quantdrent/Rien-Prescript-Beeper/firmware/ESP32/PrescriptBeeper/PixelifySans_Regular12pt7b.h

const uint8_t PixelifySans_Regular12pt7bBitmaps[] PROGMEM = {
  0x00, 0xFF, 0xFF, 0xFC, 0x3C, 0xC6, 0xC6, 0x21, 0x42, 0x30, 0xC3, 0x0C,
  0x30, 0xC3, 0x0C, 0x30, 0xCF, 0xFF, 0xFF, 0xF3, 0x0C, 0x30, 0xC3, 0x0C,
  0x30, 0xCF, 0xFF, 0xFF, 0xF3, 0x0C, 0x30, 0xC0, 0x06, 0x00, 0xC0, 0xFE,
  0x1F, 0xCC, 0x07, 0x80, 0xF0, 0x06, 0x00, 0xC0, 0x07, 0xF0, 0xFE, 0x00,
  0x30, 0x07, 0x80, 0xF0, 0x19, 0xFC, 0x3F, 0x80, 0xC0, 0x18, 0x03, 0x00,
  0x30, 0x03, 0x18, 0x01, 0xBF, 0x03, 0x1F, 0x81, 0x83, 0x07, 0x01, 0x83,
  0x00, 0x02, 0x00, 0x03, 0x00, 0x01, 0x80, 0x03, 0x03, 0x01, 0x81, 0x83,
  0x03, 0xF1, 0x81, 0xFB, 0x00, 0x31, 0x80, 0x18, 0x3F, 0x03, 0xF0, 0xC0,
  0xCC, 0x0C, 0x41, 0x03, 0x30, 0x33, 0x00, 0xC0, 0x0C, 0x03, 0x30, 0x33,
  0x0C, 0x0C, 0xC0, 0xC3, 0xF3, 0x3F, 0x30, 0xD8, 0xA0, 0x06, 0x0C, 0x18,
  0x31, 0x83, 0x06, 0x0C, 0x19, 0xC3, 0x06, 0x0C, 0x07, 0x06, 0x0C, 0x18,
  0x0C, 0x18, 0x30, 0x60, 0xC0, 0xC3, 0x0C, 0x30, 0x30, 0xC3, 0x0C, 0x30,
  0x30, 0xC3, 0x0C, 0xC3, 0x0C, 0x33, 0x0C, 0x30, 0xC3, 0x00, 0x5D, 0x50,
  0x0C, 0x03, 0x00, 0xC0, 0x30, 0x0C, 0x3F, 0xFF, 0xFC, 0x30, 0x0C, 0x03,
  0x00, 0xC0, 0xD8, 0xA0, 0xFF, 0xFC, 0xF0, 0x00, 0xC0, 0x60, 0x18, 0x0C,
  0x03, 0x01, 0x80, 0x60, 0x30, 0x0C, 0x06, 0x01, 0x80, 0xC0, 0x30, 0x18,
  0x06, 0x00, 0x3F, 0x87, 0xF3, 0x01, 0xE0, 0x3C, 0x07, 0x80, 0xF0, 0x1E,
  0x03, 0xC0, 0x78, 0x0F, 0x01, 0xE0, 0x3C, 0x06, 0x7F, 0x0F, 0xE0, 0x18,
  0x33, 0x9E, 0x30, 0x60, 0xC1, 0x83, 0x06, 0x0C, 0x18, 0x30, 0x60, 0xC1,
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
  {   616,  11,  15,  14,    1,  -14 },   // 0x47 'G'
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

const GFXfont PixelifySans_Regular12pt7b PROGMEM = {
  (uint8_t  *)PixelifySans_Regular12pt7bBitmaps,
  (GFXglyph *)PixelifySans_Regular12pt7bGlyphs,
  0x20, 0x7E, 24 };

// Approx. 2253 bytes
