quantdrent/Rien-Prescript-Beeper/firmware/ESP32/PrescriptBeeper/PixelifySans_Regular20pt7b.h

const uint8_t PixelifySans_Regular20pt7bBitmaps[] PROGMEM = {
  0x00, 0xFF, 0xFF, 0xFF, 0xFF, 0xFF, 0xFF, 0xFF, 0xFF, 0xFF, 0x00, 0x0F,
  0xFF, 0xF0, 0xF0, 0xF3, 0xC3, 0xCF, 0x0F, 0x3C, 0x3C, 0x0C, 0x0C, 0x30,
  0x33, 0x03, 0x0C, 0x0C, 0x1E, 0x07, 0x81, 0xE0, 0x78, 0x1E, 0x07, 0x81,
  0xE0, 0x78, 0x1E, 0x07, 0x81, 0xE0, 0x78, 0x1E, 0x07, 0x8F, 0xFF, 0xFF,
  0xFF, 0xFF, 0xFF, 0xFF, 0xFF, 0xFF, 0xFF, 0xF1, 0xE0, 0x78, 0x1E, 0x07,
  0x81, 0xE0, 0x78, 0x1E, 0x07, 0x81, 0xE0, 0x78, 0x1E, 0x07, 0x81, 0xE0,
  0x78, 0xFF, 0xFF, 0xFF, 0xFF, 0xFF, 0xFF, 0xFF, 0xFF, 0xFF, 0xFF, 0x1E,
  0x07, 0x81, 0xE0, 0x78, 0x1E, 0x07, 0x80, 0x00, 0xF0, 0x00, 0x3C, 0x00,
  0x0F, 0x00, 0x3F, 0xF8, 0x0F, 0xFE, 0x03, 0xFF, 0x80, 0xFF, 0xE3, 0xC0,
  0x0F, 0xF0, 0x03, 0xFC, 0x00, 0xFF, 0x00, 0x3F, 0xC0, 0x00, 0xF0, 0x00,
  0x3C, 0x00, 0x00, 0xFF, 0xE0, 0x3F, 0xF8, 0x0F, 0xFE, 0x03, 0xFF, 0x80,
  0x00, 0x3C, 0x00, 0x0F, 0xF0, 0x03, 0xFC, 0x00, 0xFF, 0x00, 0x3F, 0xC0,
  0x0F, 0x0F, 0xFE, 0x03, 0xFF, 0x80, 0xFF, 0xE0, 0x3F, 0xF8, 0x00, 0xF0,
  0x00, 0x3C, 0x00, 0x0F, 0x00, 0x1E, 0x00, 0x01, 0xE1, 0xE0, 0x00, 0x1E,
  0x1E, 0x00, 0x01, 0xE1, 0xE0, 0x00, 0x1E, 0xFF, 0xC0, 0x1E, 0x0F, 0xFC,
  0x01, 0xE0, 0xFF, 0xC0, 0x1E, 0x0F, 0xFC, 0x01, 0xE0, 0x1E, 0x01, 0xE0,
  0x01, 0xE0, 0x1E, 0x00, 0x1E, 0x1F, 0xE0, 0x01, 0xE1, 0xFE, 0x00, 0x00,
  0x1E, 0x00, 0x00, 0x01, 0xE0, 0x00, 0x00, 0xF0, 0x07, 0x80, 0x0F, 0x00,
  0x78, 0x00, 0xF0, 0x07, 0x80, 0x7F, 0x03, 0xFF, 0x07, 0x80, 0x3F, 0xF0,
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
  {  1703,  18,  25,  23,    2,  -24 },   // 0x47 'G'
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

const GFXfont PixelifySans_Regular20pt7b PROGMEM = {
  (uint8_t  *)PixelifySans_Regular20pt7bBitmaps,
  (GFXglyph *)PixelifySans_Regular20pt7bGlyphs,
  0x20, 0x7E, 39 };

// Approx. 5065 bytes
