quantdrent/Rien-Prescript-Beeper/firmware/ESP32/PrescriptBeeper/PixelifySans_Regular9pt7b.h

const uint8_t PixelifySans_Regular9pt7bBitmaps[] PROGMEM = {
  0x00, 0xFF, 0xFF, 0x3C, 0xCD, 0x98, 0x8A, 0x20, 0x63, 0x31, 0x98, 0xDF,
  0xFF, 0xFB, 0x19, 0x8C, 0xC6, 0xFF, 0xFF, 0xD8, 0xC0, 0x18, 0x1F, 0x0F,
  0x98, 0x3C, 0x1E, 0x00, 0xF8, 0x7C, 0x01, 0xE0, 0xF0, 0x67, 0xC3, 0xE0,
  0xC0, 0x60, 0x36, 0x03, 0xF0, 0xCF, 0x0C, 0x61, 0x86, 0x78, 0x06, 0x01,
  0x86, 0x38, 0xF3, 0x0F, 0xC0, 0x6C, 0x06, 0x3E, 0x0F, 0x8C, 0x1B, 0x06,
  0x36, 0x0D, 0x80, 0x80, 0xD8, 0xF7, 0xB0, 0x63, 0xEC, 0xFB, 0xD8, 0xA0,
  0x18, 0xC6, 0x36, 0x31, 0x98, 0xC6, 0x18, 0xC6, 0x3C, 0x63, 0x18, 0xC6,
  0x31, 0x83, 0x18, 0xC3, 0x18, 0xCC, 0x63, 0x7B, 0x18, 0xC0, 0xEA, 0x80,
  0x18, 0x18, 0x18, 0xFF, 0xFF, 0x18, 0x18, 0xD8, 0xA0, 0xFF, 0xC0, 0xF0,
  0x02, 0x0C, 0x30, 0x61, 0x83, 0x0C, 0x18, 0x60, 0x83, 0x00, 0x3E, 0x1F,
  0x30, 0x78, 0x3C, 0x1E, 0x0F, 0x07, 0x83, 0xC1, 0xE0, 0xCF, 0x87, 0xC0,
  0x63, 0x37, 0xB1, 0x8C, 0x63, 0x18, 0xC6, 0x30, 0x3E, 0x1F, 0x30, 0x78,
  0x30, 0x19, 0xF0, 0xF9, 0x80, 0xC1, 0xE0, 0xCF, 0x87, 0xC0, 0x3E, 0x1F,
  0x30, 0x78, 0x30, 0x19, 0xF0, 0xF8, 0x03, 0xC1, 0xE0, 0xCF, 0x87, 0xC0,
  0x03, 0x81, 0xC3, 0x61, 0xB3, 0x19, 0x8F, 0x07, 0xFF, 0xFF, 0x80, 0xC0,
  0x60, 0x30, 0x3E, 0x1F, 0x30, 0x78, 0x3C, 0x19, 0x80, 0xC0, 0x1C, 0xCF,
  0xE0, 0xCF, 0x87, 0xC0, 0x3E, 0x1F, 0x30, 0x78, 0x3C, 0x07, 0xF3, 0xF9,
  0x83, 0xC1, 0xE0, 0xCF, 0x87, 0xC0, 0x3E, 0x1F, 0x30, 0x78, 0x30, 0x18,
  0x0C, 0x06, 0x03, 0x01, 0x80, 0xC0, 0x60, 0x30, 0x3E, 0x1F, 0x30, 0x78,
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
  {   402,   9,  12,  11,    1,  -11 },   // 0x47 'G'
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

const GFXfont PixelifySans_Regular9pt7b PROGMEM = {
  (uint8_t  *)PixelifySans_Regular9pt7bBitmaps,
  (GFXglyph *)PixelifySans_Regular9pt7bGlyphs,
  0x20, 0x7E, 18 };

// Approx. 1685 bytes
